mornepousse/Mase/MaSe_firmware/main/main.c

/*
 * SPDX-FileCopyrightText: 2022-2024 Espressif Systems (Shanghai) CO LTD
 *
 * SPDX-License-Identifier: Unlicense OR CC0-1.0
 */

#include <stdlib.h>
#include "esp_log.h"
#include "freertos/FreeRTOS.h"
#include "freertos/task.h"
#include "tinyusb.h"
#include "class/hid/hid_device.h"
#include "driver/gpio.h"



void app_main(void)
{
   
}
