mornepousse/Mase/MaSe_CoDe/main/srom_pmw3389.h

#pragma once
#include <stdint.h>

#define PRODUCT_ID 0x00
#define REVISION_ID 0x01
#define MOTION 0x02
#define DELTA_X_L 0x03
#define DELTA_X_H 0x04
#define DELTA_Y_L 0x05
#define DELTA_Y_H 0x06
#define SQUAL 0x07
#define RAWDATA_SUM 0x08
#define MAXIMUM_RAWDATA 0x09
#define MINIMUM_RAWDATA 0x0A
#define SHUTTER_LOWER 0x0B
#define SHUTTER_UPPER 0x0C
#define RIPPLE_CONTROL 0x0D
#define RESOLUTION_L 0x0E
#define RESOLUTION_H 0x0F
#define CONFIG_2 0x10
#define ANGLE_TUNE 0x11
#define FRAME_CAPTURE 0x12
#define SROM_ENABLE 0x13
#define RUN_DOWNSHIFT 0x14
#define REST1_RATE_LOWER 0x15
#define REST1_RATE_UPPER 0x16
#define REST1_DOWNSHIFT 0x17
#define REST2_RATE_LOWER 0x18
#define REST2_RATE_UPPER 0x19
#define REST2_DOWNSHIFT 0x1A
#define REST3_RATE_LOWER 0x1B
#define REST3_RATE_UPPER 0x1C
#define OBSERVATION 0x24
#define DATA_OUT_LOWER 0x25
#define DATA_OUT_UPPER 0x26
#define SROM_ID 0x2A
#define MIN_SQ_ID 0x2B
#define RAWDATA_THRESHOLD 0x2C
#define CONTROL2 0x2D
#define CONFIG5_L 0x2E
#define CONFIG5_H 0x2F
#define POWER_UP_RESET 0x3A
#define SHUTDOWN 0x3B
#define INVERSE_PRODUCT_ID 0x3F
#define LIFTCUTOLL_CAL3 0x41
#define ANGLE_SNAP 0x42
#define LIFTCUTOFF_CAL1 0x4A
#define MOTION_BURST 0x50
#define SROM_LOAD_BURST 0x62
#define LIFTCUTOFF_CAL2 0x65
#define LIFTCUTOFF_CAL_TIMEOUT 0x71
#define LIFTCUTOFF_CAL_MIN_LENGTH 0x72
#define PWM_PERIOD_CNT 0x73
#define PWM_WIDTH_CNT 0x74



// Exemple simplifié, à remplacer par ton vrai tableau depuis SROM_PMW3389.ino
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
0x66, 0x6f, 0x3c, 0x8e, 0x2d, 0x82, 0x97, 0x9f, 0x4a, 0x01, 0xdc, 0x99, 0x98, 0x00, 0xec, 
0x38, 0x7a, 0x79, 0x70, 0xa6, 0x85, 0xd6, 0x21, 0x63, 0x0d, 0x45, 0x9a, 0x2e, 0x5e, 0xa7, 
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
};

const int srom_length = sizeof(srom_firmware);
